cyses/Nova-IOT/App Gui/includes/classes/PhpSpreadsheet/Documentation/assets/ClassDiagrams/Exports/ReaderWriter.png

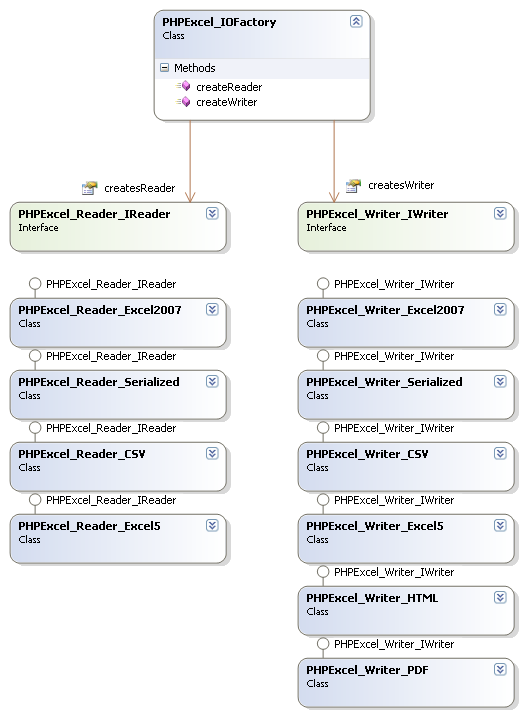
App Gui/includes/classes/PhpSpreadsheet/Documentation/assets/ClassDiagrams/Exports/ReaderWriter.png
