cyses/Nova-IOT/App Gui/includes/classes/PhpSpreadsheet/Documentation/assets/ClassDiagrams/ReaderWriter.png

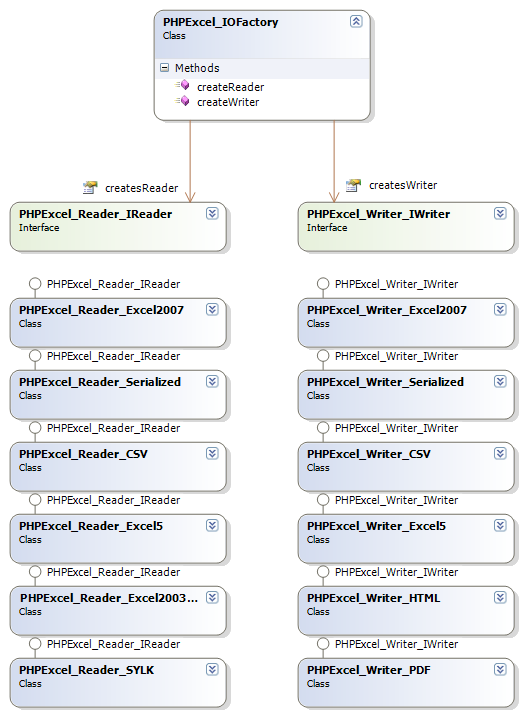
App Gui/includes/classes/PhpSpreadsheet/Documentation/assets/ClassDiagrams/ReaderWriter.png
