cyses/Nova-IOT/App Gui/includes/classes/PhpSpreadsheet/Documentation/markdown/Features/Autofilters/images/01-01-autofilter.png

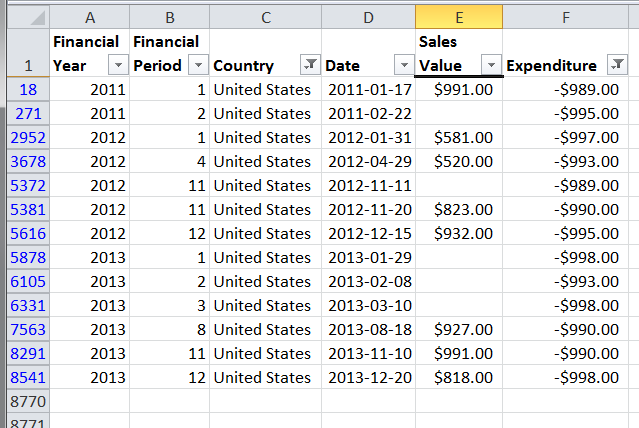
App Gui/includes/classes/PhpSpreadsheet/Documentation/markdown/Features/Autofilters/images/01-01-autofilter.png
