cyses/Nova-IOT/App Gui/includes/classes/PhpSpreadsheet/Documentation/markdown/Features/Autofilters/images/04-01-simple-autofilter.png

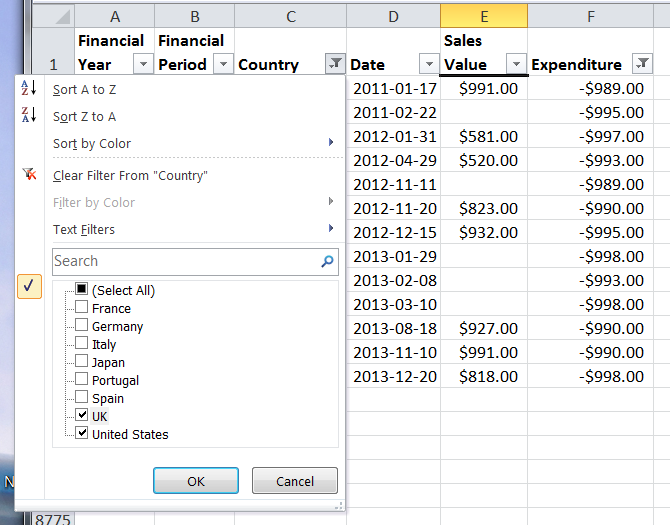
App Gui/includes/classes/PhpSpreadsheet/Documentation/markdown/Features/Autofilters/images/04-01-simple-autofilter.png
