cyses/Nova-IOT/App Gui/includes/classes/PhpSpreadsheet/Documentation/markdown/Features/Autofilters/images/04-02-dategroup-autofilter.png

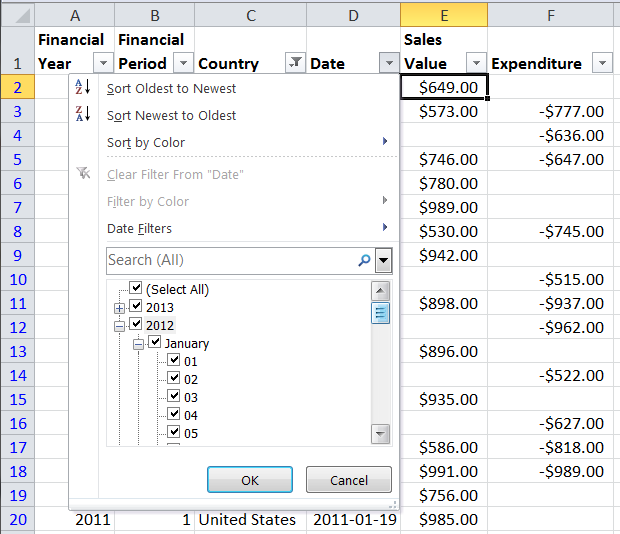
App Gui/includes/classes/PhpSpreadsheet/Documentation/markdown/Features/Autofilters/images/04-02-dategroup-autofilter.png
