cyses/Nova-IOT/App Gui/includes/classes/PhpSpreadsheet/Documentation/markdown/Overview/images/07-simple-example-4.png

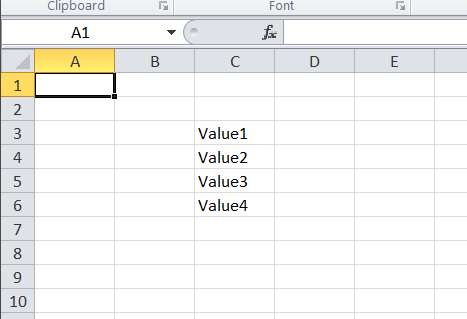
App Gui/includes/classes/PhpSpreadsheet/Documentation/markdown/Overview/images/07-simple-example-4.png
