cyses/Nova-IOT/App Gui/includes/classes/PhpSpreadsheet/Documentation/markdown/Overview/images/08-styling-border-options.png

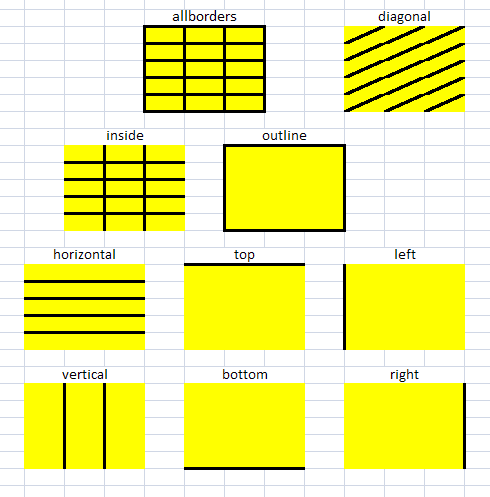
App Gui/includes/classes/PhpSpreadsheet/Documentation/markdown/Overview/images/08-styling-border-options.png
