cyses/Nova-IOT/App Gui/includes/classes/PhpSpreadsheet/Documentation/markdown/Overview/images/09-formula-in-cell-1.png

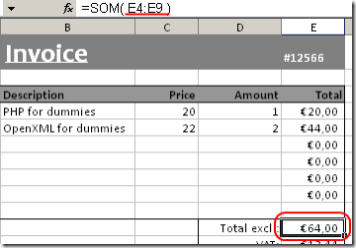
App Gui/includes/classes/PhpSpreadsheet/Documentation/markdown/Overview/images/09-formula-in-cell-1.png
