cyses/Nova-IOT/App Gui/includes/classes/PhpSpreadsheet/Documentation/markdown/Overview/images/08-page-setup-margins.png

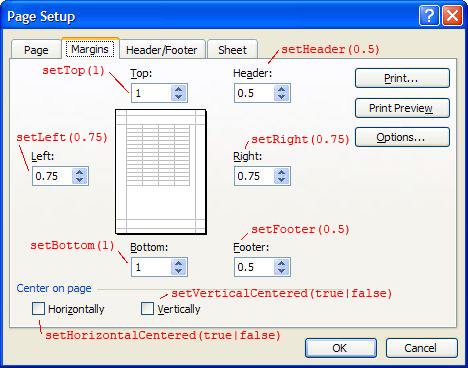
App Gui/includes/classes/PhpSpreadsheet/Documentation/markdown/Overview/images/08-page-setup-margins.png
