cyses/Nova-IOT/App Gui/includes/classes/PhpSpreadsheet/Documentation/markdown/Overview/images/08-page-setup-scaling-options.png

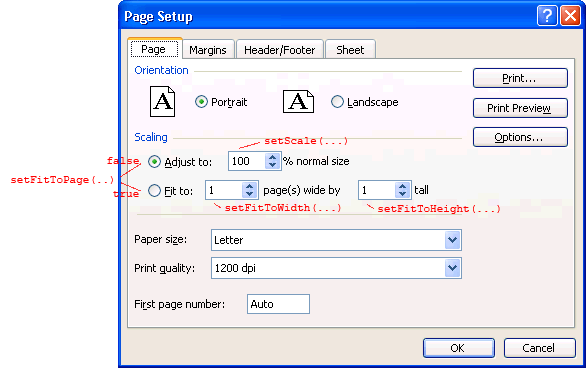
App Gui/includes/classes/PhpSpreadsheet/Documentation/markdown/Overview/images/08-page-setup-scaling-options.png
